sctanf/Bigscreen-Beyond-Valve-Index-Strap-Adapter/images/DSC_0304.jpg

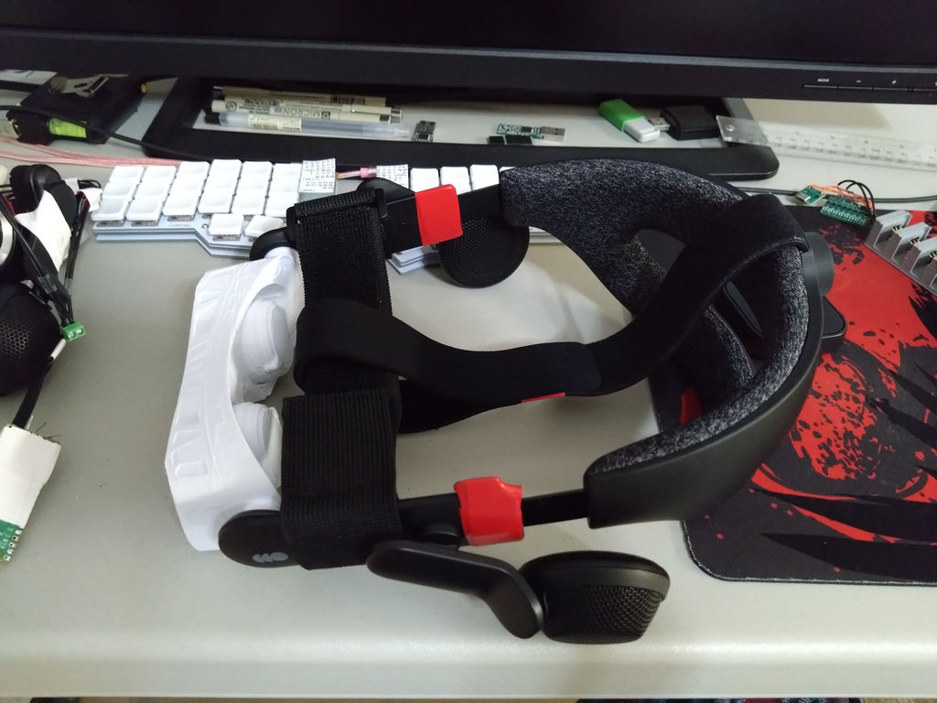
images/DSC_0304.jpg
