sctanf/Bigscreen-Beyond-Valve-Index-Strap-Adapter/images/DSC_0445.jpg

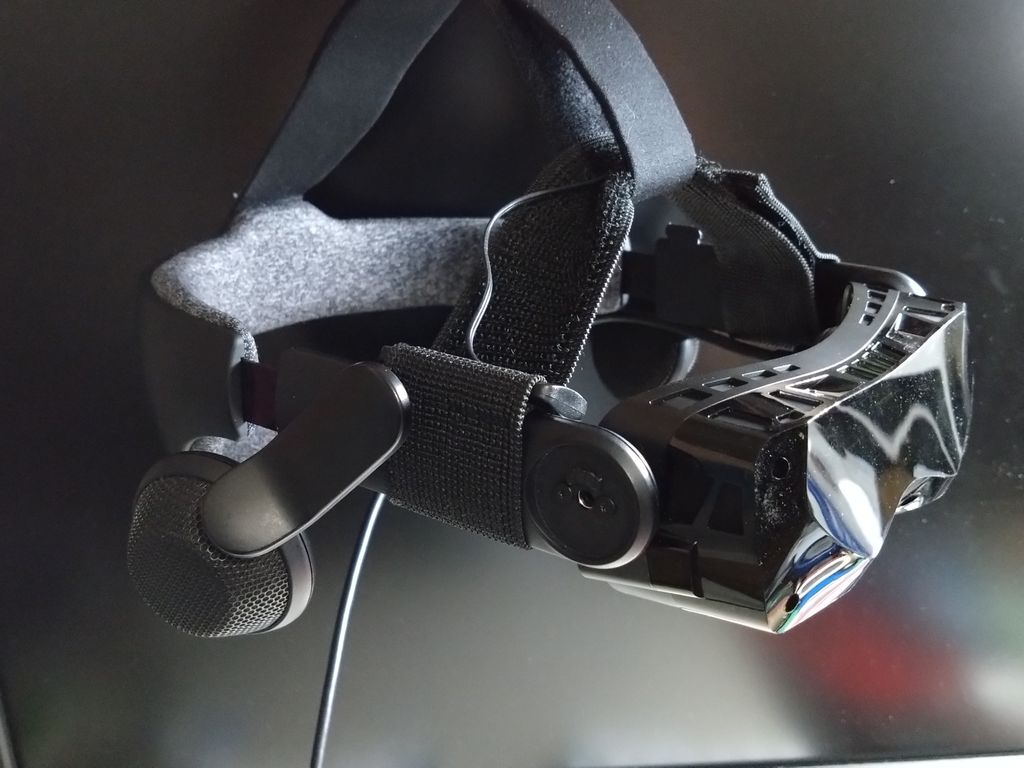
images/DSC_0445.jpg
